voltversa/Advanced-Smart-Home-Hub/submission/Mahmoud_Mostafa_Adv_pcb/07_SmartHomeHub_Schematic_ERC_RevA.pdf

### Electrical Rules Check Report

Class | Document | Message
Warning | Sheet2.SchDoc | Off grid Pin F1-2 at 97.78mm,165mm
Warning | Sheet1.SchDoc | Off grid Pin IC1-3 at 55.08mm,25mm
Warning | Sheet1.SchDoc | Off grid Pin IC1-4 at 57.62mm,25mm
Warning | Sheet2.SchDoc | Off grid Pin C62-1 at 197.3mm,110mm
Warning | Sheet2.SchDoc | Off grid Pin D1-2 at 105mm,149.76mm
Warning | Sheet5.SchDoc | Off grid Pin D2-2 at 129.76mm,120mm
Warning | Sheet1.SchDoc | Off grid Pin IC1-5 at 60.16mm,25mm
Warning | Sheet1.SchDoc | Off grid Pin IC1-9 at 70.32mm,25mm
Warning | Sheet1.SchDoc | Off grid Pin IC1-10 at 72.86mm,25mm
Warning | Sheet1.SchDoc | Off grid Pin IC1-11 at 75.4mm,25mm
Warning | Sheet1.SchDoc | Off grid Pin IC1-6 at 62.7mm,25mm
Warning | Sheet1.SchDoc | Off grid Pin IC1-7 at 65.24mm,25mm
Warning | Sheet1.SchDoc | Off grid Pin IC1-8 at 67.78mm,25mm
Warning | Sheet2.SchDoc | Off grid Pin C61-1 at 252.7mm,145mm
Warning | Sheet3.SchDoc | Off grid Pin C51-1 at 160mm,62.3mm
Warning | Sheet3.SchDoc | Off grid Pin C52-1 at 170mm,62.3mm
Warning | Sheet2.SchDoc | Off grid Pin C53-1 at 70mm,107.3mm
Warning | Sheet2.SchDoc | Off grid Pin C48-1 at 60mm,107.3mm
Warning | Sheet3.SchDoc | Off grid Pin C49-1 at 140mm,62.3mm
Warning | Sheet3.SchDoc | Off grid Pin C50-1 at 150mm,62.3mm
Warning | Sheet5.SchDoc | Off grid Pin C54-1 at 30mm,82.3mm
Warning | Sheet3.SchDoc | Off grid Pin C58-1 at 190mm,62.3mm
Warning | Sheet6.SchDoc | Off grid Pin C59-2 at 80mm,69.92mm
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
Warning | Sheet1.SchDoc | Off grid Pin IC1-62 at 197.32mm,55.48mm
Warning | Sheet1.SchDoc | Off grid Pin IC1-66 at 197.32mm,65.64mm
Warning | Sheet1.SchDoc | Off grid Pin IC1-70 at 197.32mm,75.8mm
Warning | Sheet1.SchDoc | Off grid Pin IC1-71 at 197.32mm,78.34mm
Warning | Sheet1.SchDoc | Off grid Pin IC1-72 at 197.32mm,80.88mm
Warning | Sheet1.SchDoc | Off grid Pin IC1-67 at 197.32mm,68.18mm
Warning | Sheet1.SchDoc | Off grid Pin IC1-68 at 197.32mm,70.72mm
Warning | Sheet1.SchDoc | Off grid Pin IC1-69 at 197.32mm,73.26mm
Warning | Sheet1.SchDoc | Off grid Pin IC1-59 at 197.32mm,47.86mm
Warning | Sheet1.SchDoc | Off grid Pin IC1-48 at 169.38mm,25mm
Warning | Sheet1.SchDoc | Off grid Pin IC1-49 at 171.92mm,25mm
Warning | Sheet1.SchDoc | Off grid Pin IC1-50 at 174.46mm,25mm
Warning | Sheet1.SchDoc | Off grid Pin IC1-45 at 161.76mm,25mm
Warning | Sheet1.SchDoc | Off grid Pin IC1-46 at 164.3mm,25mm
Warning | Sheet1.SchDoc | Off grid Pin IC1-47 at 166.84mm,25mm
Warning | Sheet1.SchDoc | Off grid Pin IC1-52 at 179.54mm,25mm
Warning | Sheet1.SchDoc | Off grid Pin IC1-56 at 197.32mm,40.24mm
Warning | Sheet1.SchDoc | Off grid Pin IC1-57 at 197.32mm,42.78mm
Warning | Sheet1.SchDoc | Off grid Pin IC1-58 at 197.32mm,45.32mm
Warning | Sheet1.SchDoc | Off grid Pin IC1-53 at 197.32mm,32.62mm
Warning | Sheet1.SchDoc | Off grid Pin IC1-54 at 197.32mm,35.16mm
Warning | Sheet1.SchDoc | Off grid Pin IC1-55 at 197.32mm,37.7mm
Warning | Sheet1.SchDoc | Off grid Pin IC1-73 at 197.32mm,83.42mm
Warning | Sheet1.SchDoc | Off grid Pin IC1-91 at 197.32mm,129.14mm
Warning | Sheet1.SchDoc | Off grid Pin IC1-92 at 197.32mm,131.68mm
Warning | Sheet1.SchDoc | Off grid Pin IC1-93 at 197.32mm,134.22mm
Warning | Sheet1.SchDoc | Off grid Pin IC1-88 at 197.32mm,121.52mm
Warning | Sheet1.SchDoc | Off grid Pin IC1-89 at 197.32mm,124.06mm

Warning | Sheet1.SchDoc | Off grid Pin IC1-90 at 197.32mm,126.6mm
Warning | Sheet1.SchDoc | Off grid Pin IC1-94 at 197.32mm,136.76mm
Warning | Sheet1.SchDoc | Off grid Pin IC1-98 at 197.32mm,146.92mm
Warning | Sheet1.SchDoc | Off grid Pin IC1-99 at 197.32mm,149.46mm
Warning | Sheet1.SchDoc | Off grid Pin IC1-100 at 197.32mm,152mm
Warning | Sheet1.SchDoc | Off grid Pin IC1-95 at 197.32mm,139.3mm
Warning | Sheet1.SchDoc | Off grid Pin IC1-96 at 197.32mm,141.84mm
Warning | Sheet1.SchDoc | Off grid Pin IC1-97 at 197.32mm,144.38mm
Warning | Sheet1.SchDoc | Off grid Pin IC1-87 at 197.32mm,118.98mm
Warning | Sheet1.SchDoc | Off grid Pin IC1-77 at 197.32mm,93.58mm
Warning | Sheet1.SchDoc | Off grid Pin IC1-78 at 197.32mm,96.12mm
Warning | Sheet1.SchDoc | Off grid Pin IC1-79 at 197.32mm,98.66mm
Warning | Sheet1.SchDoc | Off grid Pin IC1-74 at 197.32mm,85.96mm
Warning | Sheet1.SchDoc | Off grid Pin IC1-75 at 197.32mm,88.5mm
Warning | Sheet1.SchDoc | Off grid Pin IC1-76 at 197.32mm,91.04mm
Warning | Sheet1.SchDoc | Off grid Pin IC1-80 at 197.32mm,101.2mm
Warning | Sheet1.SchDoc | Off grid Pin IC1-84 at 197.32mm,111.36mm
Warning | Sheet1.SchDoc | Off grid Pin IC1-85 at 197.32mm,113.9mm
Warning | Sheet1.SchDoc | Off grid Pin IC1-86 at 197.32mm,116.44mm
Warning | Sheet1.SchDoc | Off grid Pin IC1-81 at 197.32mm,103.74mm
Warning | Sheet1.SchDoc | Off grid Pin IC1-82 at 197.32mm,106.28mm
Warning | Sheet1.SchDoc | Off grid Pin IC1-83 at 197.32mm,108.82mm
Warning | Sheet1.SchDoc | Off grid Net Label SWO at 20mm,73.26mm
Warning | Sheet1.SchDoc | Off grid Net Label LCD_B3 at 20mm,103.74mm
Warning | Sheet5.SchDoc | Off grid Net Label LCD_B3 at 206.58mm,147.14mm
Warning | Sheet1.SchDoc | Off grid Net Label LCD_B4 at 20mm,40.24mm
Warning | Sheet5.SchDoc | Off grid Net Label LCD_B1 at 211.66mm,147.14mm
Warning | Sheet1.SchDoc | Off grid Net Label LCD_B2 at 20mm,124.06mm
Warning | Sheet5.SchDoc | Off grid Net Label LCD_B2 at 209.12mm,147.14mm
Warning | Sheet5.SchDoc | Off grid Net Label LCD_B4 at 204.04mm,147.14mm
Warning | Sheet5.SchDoc | Off grid Net Label LCD_B6 at 198.96mm,147.14mm
Warning | Sheet1.SchDoc | Off grid Net Label LCD_B7 at 20mm,80.88mm
Warning | Sheet5.SchDoc | Off grid Net Label LCD_B7 at 196.42mm,147.14mm
Warning | Sheet1.SchDoc | Off grid Net Label LCD_B5 at 174.46mm,11.68mm
Warning | Sheet5.SchDoc | Off grid Net Label LCD_B5 at 201.5mm,147.14mm
Warning | Sheet1.SchDoc | Off grid Net Label LCD_B6 at 20mm,83.42mm
Warning | Sheet1.SchDoc | Off grid Net Label LCD_B1 at 20mm,101.2mm
Warning | Sheet4.SchDoc | Off grid LED1 at 139.76mm,100mm
Warning | Sheet5.SchDoc | Off grid LED2 at 115.24mm,35mm
Warning | Sheet2.SchDoc | Off grid Net Label D+ at 30mm,144.52mm
Warning | Sheet2.SchDoc | Off grid C62 at 197.3mm,110mm
Warning | Sheet2.SchDoc | Off grid J4 at 19.84mm,139.44mm
Warning | Sheet2.SchDoc | Off grid L3 at 125.08mm,127.54mm
Warning | Sheet2.SchDoc | Off grid Net Label D- at 30mm,147.06mm
Warning | Sheet5.SchDoc | Off grid Net Label GND at 193.88mm,147.14mm
Warning | Sheet1.SchDoc | Off grid Net Label LCD_B0 at 55.08mm,15mm
Warning | Sheet5.SchDoc | Off grid Net Label LCD_B0 at 214.2mm,147.14mm
Warning | Sheet1.SchDoc | Off grid Net Label ESP_RX at 250mm,33.87mm
Warning | Sheet1.SchDoc | Off grid Net Label ESP_TX at 80.48mm,175mm
Warning | Sheet1.SchDoc | Off grid Net Label ESP_TX at 250mm,38.23mm
Warning | Sheet1.SchDoc | Off grid Net Label LCD_BL_CTRL at 90.64mm,170mm
Warning | Sheet5.SchDoc | Off grid Net Label LCD_G4 at 224.36mm,147.14mm
Warning | Sheet1.SchDoc | Off grid Net Label LCD_G5 at 210mm,129.14mm
Warning | Sheet5.SchDoc | Off grid Net Label LCD_G5 at 221.82mm,147.14mm
Warning | Sheet1.SchDoc | Off grid Net Label LCD_G3 at 20mm,106.28mm
Warning | Sheet5.SchDoc | Off grid Net Label LCD_G3 at 226.9mm,147.14mm
Warning | Sheet1.SchDoc | Off grid Net Label LCD_G4 at 200mm,126.6mm
Warning | Sheet1.SchDoc | Off grid Net Label LCD_G6 at 93.18mm,175mm
Warning | Sheet1.SchDoc | Off grid Net Label LCD_HSYNC at 77.94mm,10mm
Warning | Sheet5.SchDoc | Off grid Net Label LCD_HSYNC at 186.26mm,147.14mm
Warning | Sheet5.SchDoc | Off grid Net Label LCD_INT at 105.4mm,167.46mm
Warning | Sheet5.SchDoc | Off grid Net Label LCD_G6 at 219.28mm,147.14mm
Warning | Sheet1.SchDoc | Off grid Net Label LCD_G7 at 20mm,136.76mm
Warning | Sheet5.SchDoc | Off grid Net Label LCD_G7 at 216.74mm,147.14mm
Warning | Sheet5.SchDoc | Off grid Net Label LCD_G2 at 229.44mm,147.14mm
Warning | Sheet1.SchDoc | Off grid Net Label LCD_DCLK at 270mm,80.08mm
Warning | Sheet1.SchDoc | Off grid Net Label LCD_DE at 20mm,78.34mm
Warning | Sheet5.SchDoc | Off grid Net Label LCD_DE at 181.18mm,147.14mm

Warning | Sheet1.SchDoc | Off grid Net Label LCD_DCLK at 100.8mm,10mm
Warning | Sheet5.SchDoc | Off grid Net Label LCD_DCLK at 191.34mm,147.14mm
Warning | Sheet5.SchDoc | Off grid Net Label LCD_DCLK at 255mm,90.08mm
Warning | Sheet1.SchDoc | Off grid Net Label LCD_DISP at 20mm,96.12mm
Warning | Sheet1.SchDoc | Off grid Net Label LCD_G1 at 60.16mm,15mm
Warning | Sheet5.SchDoc | Off grid Net Label LCD_G1 at 231.98mm,147.14mm
Warning | Sheet1.SchDoc | Off grid Net Label LCD_G2 at 200mm,37.7mm
Warning | Sheet5.SchDoc | Off grid Net Label LCD_DISP at 188.8mm,147.14mm
Warning | Sheet1.SchDoc | Off grid Net Label LCD_G0 at 57.62mm,15mm
Warning | Sheet5.SchDoc | Off grid Net Label LCD_G0 at 234.52mm,147.14mm
Warning | Sheet2.SchDoc | Off grid C61 at 252.7mm,145mm
Warning | Sheet3.SchDoc | Off grid C15 at 70mm,62.3mm
Warning | Sheet3.SchDoc | Off grid C16 at 80mm,62.3mm
Warning | Sheet3.SchDoc | Off grid C17 at 90mm,62.3mm
Warning | Sheet3.SchDoc | Off grid C12 at 10mm,62.3mm
Warning | Sheet3.SchDoc | Off grid C13 at 50mm,62.3mm
Warning | Sheet3.SchDoc | Off grid C14 at 60mm,62.3mm
Warning | Sheet3.SchDoc | Off grid C18 at 100mm,62.3mm
Warning | Sheet6.SchDoc | Off grid C23 at 75mm,157.3mm
Warning | Sheet6.SchDoc | Off grid C24 at 160mm,154.76mm
Warning | Sheet6.SchDoc | Off grid C25 at 25mm,17.3mm
Warning | Sheet3.SchDoc | Off grid C19 at 110mm,62.3mm
Warning | Sheet3.SchDoc | Off grid C20 at 120mm,62.3mm
Warning | Sheet6.SchDoc | Off grid C21 at 102.7mm,125mm
Warning | Sheet3.SchDoc | Off grid C11 at 40mm,62.3mm
Warning | Sheet1.SchDoc | Nets Wire LCD_BL_CTRL has multiple names (Net Label LCD_BL_CTRL (2), Net Label
| | LCD_BL_CTRL_STM (2))
Warning | Sheet2.SchDoc | NetU1_5 contains Input Pin and Unspecified Port objects (Pin U1-5, Port PC10).
Warning | Sheet2.SchDoc | NetU1_6 contains Output Pin and Unspecified Port objects (Pin U1-6, Port PC11).
Warning | Sheet1.SchDoc | Net NetIC1_161 has no driving source (Pin IC1-161, Pin U1-5)
Warning | Sheet2.SchDoc | Net NetR24_2 has no driving source (Pin R24-2, Pin U1-4)
Warning | Sheet2.SchDoc | Net NetU1_10 has no driving source (Pin U1-10)
Warning | Sheet3.SchDoc | Off grid C2 at 50mm,102.3mm
Warning | Sheet3.SchDoc | Off grid C8 at 115mm,137.3mm
Warning | Sheet3.SchDoc | Off grid C9 at 20mm,62.3mm
Warning | Sheet3.SchDoc | Off grid C10 at 30mm,62.3mm
Warning | Sheet4.SchDoc | Off grid C4 at 85mm,107.3mm
Warning | Sheet3.SchDoc | Off grid C6 at 145mm,145.08mm
Warning | Sheet3.SchDoc | Off grid C7 at 160mm,145.08mm
Warning | Sheet6.SchDoc | Off grid C26 at 35mm,17.3mm
Warning | Sheet3.SchDoc | Off grid C50 at 150mm,62.3mm
Warning | Sheet3.SchDoc | Off grid C51 at 160mm,62.3mm
Warning | Sheet3.SchDoc | Off grid C52 at 170mm,62.3mm
Warning | Sheet2.SchDoc | Off grid C46 at 155mm,112.3mm
Warning | Sheet2.SchDoc | Off grid C48 at 60mm,107.3mm
Warning | Sheet3.SchDoc | Off grid C49 at 140mm,62.3mm
Warning | Sheet2.SchDoc | Off grid C53 at 70mm,107.3mm
Warning | Sheet6.SchDoc | Off grid C57 at 142.7mm,85mm
Warning | Sheet3.SchDoc | Off grid C58 at 190mm,62.3mm
Warning | Sheet2.SchDoc | Off grid C60 at 197.3mm,175mm
Warning | Sheet5.SchDoc | Off grid C54 at 30mm,82.3mm
Warning | Sheet6.SchDoc | Off grid C55 at 95mm,17.3mm
Warning | Sheet5.SchDoc | Off grid C56 at 115mm,137.3mm
Warning | Sheet4.SchDoc | Off grid C45 at 240mm,97.3mm
Warning | Sheet6.SchDoc | Off grid C30 at 80mm,17.3mm
Warning | Sheet4.SchDoc | Off grid C33 at 160mm,132.3mm
Warning | Sheet4.SchDoc | Off grid C36 at 170mm,132.3mm
Warning | Sheet6.SchDoc | Off grid C27 at 45mm,17.3mm
Warning | Sheet6.SchDoc | Off grid C28 at 55mm,17.3mm
Warning | Sheet6.SchDoc | Off grid C29 at 65mm,17.3mm
Warning | Sheet4.SchDoc | Off grid C37 at 75mm,112.3mm
Warning | Sheet2.SchDoc | Off grid C42 at 135mm,152.3mm
Warning | Sheet2.SchDoc | Off grid C43 at 117.7mm,135mm
Warning | Sheet4.SchDoc | Off grid C44 at 220mm,97.3mm
Warning | Sheet4.SchDoc | Off grid C39 at 180mm,32.3mm
Warning | Sheet4.SchDoc | Off grid C40 at 95mm,39.76mm
Warning | Sheet4.SchDoc | Off grid C41 at 30mm,37.3mm
Warning | Sheet5.SchDoc | Off grid Net Label LCD_INT at 171.02mm,147.14mm

Warning | Sheet1.SchDoc | Off grid Net Label SDRAM_D2 at 20mm,144.38mm
Warning | Sheet6.SchDoc | Off grid Net Label SDRAM_D2 at 185mm,132.38mm
Warning | Sheet1.SchDoc | Off grid Net Label SDRAM_D3 at 20mm,141.84mm
Warning | Sheet6.SchDoc | Off grid Net Label SDRAM_CS at 185mm,96.82mm
Warning | Sheet1.SchDoc | Off grid Net Label SDRAM_D0 at 151.6mm,169.78mm
Warning | Sheet1.SchDoc | Off grid Net Label SDRAM_D1 at 149.06mm,169.78mm
Warning | Sheet6.SchDoc | Off grid Net Label SDRAM_D3 at 185mm,127.3mm
Warning | Sheet1.SchDoc | Off grid Net Label SDRAM_D5 at 200mm,101.2mm
Warning | Sheet6.SchDoc | Off grid Net Label SDRAM_D6 at 185mm,117.14mm
Warning | Sheet1.SchDoc | Off grid Net Label SDRAM_D6 at 210mm,103.74mm
Warning | Sheet6.SchDoc | Off grid Net Label SDRAM_D4 at 185mm,124.76mm
Warning | Sheet1.SchDoc | Off grid Net Label SDRAM_D4 at 200mm,98.66mm
Warning | Sheet6.SchDoc | Off grid Net Label SDRAM_D5 at 185mm,119.68mm
Warning | Sheet1.SchDoc | Off grid Net Label SDRAM_CS at 141.44mm,12.78mm
Warning | Sheet6.SchDoc | Off grid Net Label SDRAM_BA1 at 185mm,91.74mm
Warning | Sheet1.SchDoc | Off grid Net Label SDRAM_CAS at 15mm,75.8mm
Warning | Sheet6.SchDoc | Off grid Net Label SDRAM_CAS at 185mm,101.9mm
Warning | Sheet6.SchDoc | Off grid Net Label SDRAM_A11 at 233.02mm,94.28mm
Warning | Sheet1.SchDoc | Off grid Net Label SDRAM_BA0 at 113.5mm,170mm
Warning | Sheet6.SchDoc | Off grid Net Label SDRAM_BA0 at 185mm,94.28mm
Warning | Sheet6.SchDoc | Off grid Net Label SDRAM_CKE at 153.02mm,29.92mm
Warning | Sheet6.SchDoc | Off grid Net Label SDRAM_CLK at 153.02mm,32.46mm
Warning | Sheet6.SchDoc | Off grid Net Label SDRAM_CLK at 233.02mm,101.9mm
Warning | Sheet1.SchDoc | Off grid Net Label SDRAM_CLK at 268.02mm,112.46mm
Warning | Sheet6.SchDoc | Off grid Net Label SDRAM_CKE at 233.02mm,99.36mm
Warning | Sheet1.SchDoc | Off grid Net Label SDRAM_CKE at 268.02mm,109.92mm
Warning | Sheet1.SchDoc | Off grid Net Label SDRAM_CLK at 103.34mm,175mm
Warning | Sheet6.SchDoc | Off grid Net Label SDRAM_D7 at 185mm,112.06mm
Warning | Sheet6.SchDoc | Off grid Net Label SDRAM_RAS at 155mm,34.92mm
Warning | Sheet6.SchDoc | Off grid Net Label SDRAM_RAS at 185mm,99.36mm
Warning | Sheet1.SchDoc | Off grid Net Label SDRAM_RAS at 200mm,75.8mm
Warning | Sheet1.SchDoc | Off grid Net Label SDRAM_D15 at 166.84mm,170mm
Warning | Sheet1.SchDoc | Off grid Net Label SDRAM_LDQM at 15mm,52.94mm
Warning | Sheet1.SchDoc | Off grid Net Label SDRAM_LDQM at 265mm,102.84mm
Warning | Sheet1.SchDoc | Off grid Net Label SDRAM_RAS at 270mm,114.92mm
Warning | Sheet1.SchDoc | Off grid Net Label SWCLK at 20mm,157.08mm
Warning | Sheet1.SchDoc | Off grid Net Label SWCLK at 250mm,21.77mm
Warning | Sheet1.SchDoc | Off grid Net Label SWDIO at 72.86mm,180mm
Warning | Sheet1.SchDoc | Off grid Net Label SDRAM_UDQM at 15mm,50.4mm
Warning | Sheet1.SchDoc | Off grid Net Label SDRAM_WE at 171.92mm,10mm
Warning | Sheet6.SchDoc | Off grid Net Label SDRAM_WE at 185mm,104.44mm
Warning | Sheet6.SchDoc | Off grid Net Label SDRAM_D14 at 233.02mm,134.92mm
Warning | Sheet1.SchDoc | Off grid Net Label SDRAM_D9 at 200mm,116.44mm
Warning | Sheet6.SchDoc | Off grid Net Label SDRAM_D9 at 233.02mm,117.14mm
Warning | Sheet6.SchDoc | Off grid Net Label SDRAM_D10 at 233.02mm,119.68mm
Warning | Sheet1.SchDoc | Off grid Net Label SDRAM_D7 at 200mm,111.36mm
Warning | Sheet1.SchDoc | Off grid Net Label SDRAM_D8 at 200mm,113.9mm
Warning | Sheet6.SchDoc | Off grid Net Label SDRAM_D8 at 233.02mm,112.06mm
Warning | Sheet1.SchDoc | Off grid Net Label SDRAM_D11 at 200mm,121.52mm
Warning | Sheet1.SchDoc | Off grid Net Label SDRAM_D13 at 171.92mm,170mm
Warning | Sheet6.SchDoc | Off grid Net Label SDRAM_D13 at 233.02mm,132.38mm
Warning | Sheet1.SchDoc | Off grid Net Label SDRAM_D14 at 169.38mm,170mm
Warning | Sheet6.SchDoc | Off grid Net Label SDRAM_D11 at 233.02mm,124.76mm
Warning | Sheet1.SchDoc | Off grid Net Label SDRAM_D12 at 200mm,124.06mm
Warning | Sheet6.SchDoc | Off grid Net Label SDRAM_D12 at 233.02mm,127.3mm
Warning | Sheet1.SchDoc | Off grid Net Label SDRAM_A11 at 200mm,96.12mm
Warning | Sheet1.SchDoc | Off grid Net Label LCD_R7 at 108.42mm,169.78mm
Warning | Sheet5.SchDoc | Off grid Net Label LCD_R7 at 237.06mm,147.14mm
Warning | Sheet5.SchDoc | Off grid Net Label LCD_RST at 105.4mm,162.38mm
Warning | Sheet5.SchDoc | Off grid Net Label LCD_R5 at 242.14mm,147.14mm
Warning | Sheet1.SchDoc | Off grid Net Label LCD_R6 at 200mm,55.48mm
Warning | Sheet5.SchDoc | Off grid Net Label LCD_R6 at 239.6mm,147.14mm
Warning | Sheet5.SchDoc | Off grid Net Label LCD_RST at 173.56mm,147.14mm
Warning | Sheet5.SchDoc | Off grid Net Label LCD_SCL at 105.4mm,152.22mm
Warning | Sheet5.SchDoc | Off grid Net Label LCD_SCL at 168.48mm,147.14mm
Warning | Sheet5.SchDoc | Off grid Net Label LCD_SCL at 255mm,39.92mm
Warning | Sheet1.SchDoc | Off grid Net Label LCD_RST at 200mm,42.78mm
Warning | Sheet1.SchDoc | Off grid Net Label LCD_RST at 245mm,47.38mm

Warning | Sheet5.SchDoc | Off grid Net Label LCD_RST at 255mm,32.3mm
Warning | Sheet1.SchDoc | Off grid Net Label LCD_R5 at 136.36mm,5mm
Warning | Sheet1.SchDoc | Off grid Net Label LCD_R0 at 20mm,98.66mm
Warning | Sheet5.SchDoc | Off grid Net Label LCD_R0 at 254.84mm,147.14mm
Warning | Sheet1.SchDoc | Off grid Net Label LCD_R1 at 200mm,63.1mm
Warning | Sheet1.SchDoc | Off grid Net Label LCD_INT at 205mm,45.32mm
Warning | Sheet1.SchDoc | Off grid Net Label LCD_INT at 245mm,49.92mm
Warning | Sheet5.SchDoc | Off grid Net Label LCD_INT at 255mm,34.84mm
Warning | Sheet5.SchDoc | Off grid Net Label LCD_R1 at 252.3mm,147.14mm
Warning | Sheet5.SchDoc | Off grid Net Label LCD_R3 at 247.22mm,147.14mm
Warning | Sheet1.SchDoc | Off grid Net Label LCD_R4 at 77.94mm,175mm
Warning | Sheet5.SchDoc | Off grid Net Label LCD_R4 at 244.68mm,147.14mm
Warning | Sheet1.SchDoc | Off grid Net Label LCD_R2 at 200mm,65.64mm
Warning | Sheet5.SchDoc | Off grid Net Label LCD_R2 at 249.76mm,147.14mm
Warning | Sheet1.SchDoc | Off grid Net Label LCD_R3 at 200mm,52.94mm
Warning | Sheet1.SchDoc | Off grid Net Label LCD_SDA at 20mm,55.48mm
Warning | Sheet1.SchDoc | Off grid Net Label SDRAM_A5 at 108.42mm,10mm
Warning | Sheet6.SchDoc | Off grid Net Label SDRAM_A5 at 233.02mm,81.58mm
Warning | Sheet1.SchDoc | Off grid Net Label SDRAM_A6 at 205mm,78.34mm
Warning | Sheet6.SchDoc | Off grid Net Label SDRAM_A2 at 185mm,81.58mm
Warning | Sheet1.SchDoc | Off grid Net Label SDRAM_A3 at 103.34mm,10mm
Warning | Sheet1.SchDoc | Off grid Net Label SDRAM_A4 at 105.88mm,10mm
Warning | Sheet6.SchDoc | Off grid Net Label SDRAM_A6 at 233.02mm,84.12mm
Warning | Sheet6.SchDoc | Off grid Net Label SDRAM_A9 at 233.02mm,91.74mm
Warning | Sheet6.SchDoc | Off grid Net Label SDRAM_A10 at 185mm,89.2mm
Warning | Sheet1.SchDoc | Off grid Net Label SDRAM_A10 at 200mm,93.58mm
Warning | Sheet6.SchDoc | Off grid Net Label SDRAM_A7 at 233.02mm,86.66mm
Warning | Sheet1.SchDoc | Off grid Net Label SDRAM_A8 at 200mm,88.5mm
Warning | Sheet6.SchDoc | Off grid Net Label SDRAM_A8 at 233.02mm,89.2mm
Warning | Sheet1.SchDoc | Off grid Net Label SDRAM_A2 at 93.18mm,10mm
Warning | Sheet5.SchDoc | Off grid Net Label LCD_VSYNC at 183.72mm,147.14mm
Warning | Sheet1.SchDoc | Off grid Net Label NRST at 133.82mm,15mm
Warning | Sheet1.SchDoc | Off grid Net Label QSPI_D0 at 121.12mm,10mm
Warning | Sheet5.SchDoc | Off grid Net Label LCD_SDA at 105.4mm,157.3mm
Warning | Sheet5.SchDoc | Off grid Net Label LCD_SDA at 165.94mm,147.14mm
Warning | Sheet1.SchDoc | Off grid Net Label LCD_VSYNC at 75.4mm,10mm
Warning | Sheet1.SchDoc | Off grid Net Label QSPI_D1 at 123.66mm,10mm
Warning | Sheet6.SchDoc | Off grid Net Label SDRAM_A0 at 185mm,86.66mm
Warning | Sheet1.SchDoc | Off grid Net Label SDRAM_A1 at 90.64mm,10mm
Warning | Sheet6.SchDoc | Off grid Net Label SDRAM_A1 at 185mm,84.12mm
Warning | Sheet1.SchDoc | Off grid Net Label QSPI_D2 at 118.58mm,10mm
Warning | Sheet1.SchDoc | Off grid Net Label QSPI_NCS at 20mm,65.64mm
Warning | Sheet1.SchDoc | Off grid Net Label SDRAM_A0 at 88.1mm,10mm
Warning | Sheet1.SchDoc | Off grid Pin IC1-157 at 32.22mm,162.16mm
Warning | Sheet6.SchDoc | Off grid Port ESP_TX at 160mm,56.79mm
Warning | Sheet1.SchDoc | Off grid Port ESP_TX at 231.79mm,37.98mm
Warning | Sheet4.SchDoc | Off grid Port Flamesensor_A0 at 9.46mm,50mm
Warning | Sheet1.SchDoc | Off grid Port CO2_SDA at 197.32mm,157.08mm
Warning | Sheet6.SchDoc | Off grid Port ESP_RX at 110mm,61.66mm
Warning | Sheet1.SchDoc | Off grid Port ESP_RX at 231.66mm,33.87mm
Warning | Sheet4.SchDoc | Off grid Port Flamesensor_A0 at 109.46mm,49.92mm
Warning | Sheet1.SchDoc | Off grid Port Flamesensor_D0 at 164.3mm,4.46mm
Warning | Sheet5.SchDoc | Off grid Port LCD_B[0..7] at 217.88mm,100mm
Warning | Sheet1.SchDoc | Off grid Port LCD_B[0..7] at 232.88mm,85mm
Warning | Sheet1.SchDoc | Off grid Port Flamesensor_A0 at 159.22mm,4.46mm
Warning | Sheet4.SchDoc | Off grid Port Flamesensor_D0 at 89.46mm,25mm
Warning | Sheet4.SchDoc | Off grid Port Flamesensor_D0 at 94.46mm,80mm
Warning | Sheet4.SchDoc | Off grid Port CO2_SDA at 115mm,155.32mm
Warning | Sheet6.SchDoc | Off grid Pin Y2-3 at 208.1mm,170mm
Warning | Sheet1.SchDoc | Off grid Port BME_SCL at 197.32mm,144.38mm
Warning | Sheet1.SchDoc | Off grid Port BME_SDA at 197.32mm,146.92mm
Warning | Sheet4.SchDoc | Off grid Pin VR1-S1 at 93.02mm,52.54mm
Warning | Sheet6.SchDoc | Off grid Pin Y1-2 at 65.16mm,170mm
Warning | Sheet6.SchDoc | Off grid Pin Y2-2 at 208.1mm,167.46mm
Warning | Sheet1.SchDoc | Off grid Port BUZZER at 123.66mm,169.78mm
Warning | Sheet3.SchDoc | Off grid Port cap2 at 130.69mm,150mm
Warning | Sheet4.SchDoc | Off grid Port CO2_SCL at 115mm,152.78mm
Warning | Sheet1.SchDoc | Off grid Port CO2_SCL at 197.32mm,154.54mm

Warning | Sheet3.SchDoc | Off grid Port cap1 at 150.87mm,147.7mm
Warning | Sheet1.SchDoc | Off grid Port cap1 at 197.32mm,131.68mm
Warning | Sheet1.SchDoc | Off grid Port cap2 at 70.32mm,169.78mm
Warning | Sheet1.SchDoc | Off grid Port LCD_BL_CTRL at 229.3mm,45mm
Warning | Sheet5.SchDoc | Off grid Port LCD_SCL at 240.03mm,39.92mm
Warning | Sheet1.SchDoc | Off grid Port LCD_SDA at 229.62mm,57.54mm
Warning | Sheet5.SchDoc | Off grid Port LCD_SDA at 239.62mm,42.46mm
Warning | Sheet1.SchDoc | Off grid Port LCD_R[0..7] at 232.88mm,95mm
Warning | Sheet1.SchDoc | Off grid Port LCD_RST at 230.04mm,47.38mm
Warning | Sheet5.SchDoc | Off grid Port LCD_RST at 240.04mm,32.3mm
Warning | Sheet5.SchDoc | Off grid Port LCD_VSYNC at 211.49mm,80mm
Warning | Sheet1.SchDoc | Off grid Port OSC32_IN at 70.32mm,9.63mm
Warning | Sheet1.SchDoc | Off grid Port OSC32_OUT at 72.86mm,7.36mm
Warning | Sheet1.SchDoc | Off grid Port OSC_HSE_IN at 128.74mm,6.44mm
Warning | Sheet1.SchDoc | Off grid Port LCD_VSYNC at 226.49mm,70mm
Warning | Sheet1.SchDoc | Off grid Port NRST at 254.11mm,15mm
Warning | Sheet6.SchDoc | Off grid Port OSC32_IN at 19.63mm,170mm
Warning | Sheet5.SchDoc | Off grid Port LCD_R[0..7] at 217.88mm,110mm
Warning | Sheet5.SchDoc | Off grid Port LCD_DE at 216.18mm,75mm
Warning | Sheet1.SchDoc | Off grid Port LCD_DE at 231.18mm,65mm
Warning | Sheet5.SchDoc | Off grid Port LCD_DISP at 214.3mm,70mm
Warning | Sheet5.SchDoc | Off grid Port LCD_BL_CTRL at 234.3mm,30mm
Warning | Sheet5.SchDoc | Off grid Port LCD_DCLK at 212.92mm,90mm
Warning | Sheet1.SchDoc | Off grid Port LCD_DCLK at 227.92mm,80mm
Warning | Sheet1.SchDoc | Off grid Port LCD_DISP at 229.3mm,60mm
Warning | Sheet1.SchDoc | Off grid Port LCD_HSYNC at 226.49mm,75mm
Warning | Sheet1.SchDoc | Off grid Port LCD_INT at 230.42mm,49.92mm
Warning | Sheet5.SchDoc | Off grid Port LCD_INT at 240.42mm,34.84mm
Warning | Sheet5.SchDoc | Off grid Port LCD_G[0..7] at 217.75mm,105mm
Warning | Sheet1.SchDoc | Off grid Port LCD_G[0..7] at 232.75mm,90mm
Warning | Sheet5.SchDoc | Off grid Port LCD_HSYNC at 211.49mm,85mm
Warning | Sheet2.SchDoc | Off grid Pin U1-14 at 192.06mm,153.02mm
Warning | Sheet1.SchDoc | Off grid Pin R2-2 at 15mm,37.78mm
Warning | Sheet1.SchDoc | Off grid Pin R3-1 at 247.78mm,15mm
Warning | Sheet6.SchDoc | Off grid Pin R4-1 at 175mm,62.78mm
Warning | Sheet4.SchDoc | Off grid Pin Q1-1 at 45mm,24.76mm
Warning | Sheet1.SchDoc | Off grid Pin R1-1 at 14.44mm,78.34mm
Warning | Sheet1.SchDoc | Off grid Pin R1-2 at 14.44mm,60.56mm
Warning | Sheet3.SchDoc | Off grid Pin R5-1 at 35mm,117.22mm
Warning | Sheet4.SchDoc | Off grid Pin R9-2 at 110mm,177.78mm
Warning | Sheet4.SchDoc | Off grid Pin R10-1 at 245mm,144.92mm
Warning | Sheet4.SchDoc | Off grid Pin R10-2 at 245mm,162.7mm
Warning | Sheet6.SchDoc | Off grid Pin R6-1 at 72.78mm,130mm
Warning | Sheet5.SchDoc | Off grid Pin R7-1 at 240mm,52.22mm
Warning | Sheet5.SchDoc | Off grid Pin R8-1 at 120mm,72.22mm
Warning | Sheet5.SchDoc | Off grid Pin P3-2 at 25mm,29.92mm
Warning | Sheet6.SchDoc | Off grid Pin P1-6 at 145.32mm,72.54mm
Warning | Sheet6.SchDoc | Off grid Pin P1-8 at 145.32mm,70mm
Warning | Sheet6.SchDoc | Off grid Pin P2-1 at 44.68mm,87.54mm
Warning | Sheet6.SchDoc | Off grid Pin P1-2 at 145.32mm,77.62mm
Warning | Sheet6.SchDoc | Off grid Pin P1-3 at 125mm,75.08mm
Warning | Sheet6.SchDoc | Off grid Pin P1-4 at 145.32mm,75.08mm
Warning | Sheet6.SchDoc | Off grid Pin P2-3 at 44.68mm,85mm
Warning | Sheet6.SchDoc | Off grid Pin P2-9 at 44.68mm,77.38mm
Warning | Sheet6.SchDoc | Off grid Pin P2-10 at 65mm,77.38mm
Warning | Sheet5.SchDoc | Off grid Pin P3-1 at 25mm,27.38mm
Warning | Sheet6.SchDoc | Off grid Pin P2-5 at 44.68mm,82.46mm
Warning | Sheet6.SchDoc | Off grid Pin P2-7 at 44.68mm,79.92mm
Warning | Sheet6.SchDoc | Off grid Pin P2-8 at 65mm,79.92mm
Warning | Sheet4.SchDoc | Off grid Pin R11-2 at 110mm,152.78mm
Warning | Sheet2.SchDoc | Off grid Pin U1-3 at 192.06mm,122.54mm
Warning | Sheet2.SchDoc | Off grid Pin U1-5 at 220mm,147.94mm
Warning | Sheet2.SchDoc | Off grid Pin U1-6 at 192.06mm,140.32mm
Warning | Sheet4.SchDoc | Off grid Pin R25-2 at 109.46mm,49.92mm
Warning | Sheet6.SchDoc | Off grid Pin R26-1 at 195mm,47.78mm
Warning | Sheet2.SchDoc | Off grid Pin U1-2 at 192.06mm,120mm
Warning | Sheet2.SchDoc | Off grid Pin U1-7 at 192.06mm,125.08mm
Warning | Sheet2.SchDoc | Off grid Pin U1-11 at 220mm,132.7mm

Warning | Sheet2.SchDoc | Off grid Pin U1-12 at 220mm,127.62mm
Warning | Sheet2.SchDoc | Off grid Pin U1-13 at 220mm,125.08mm
Warning | Sheet2.SchDoc | Off grid Pin U1-8 at 192.06mm,127.62mm
Warning | Sheet2.SchDoc | Off grid Pin U1-9 at 220mm,142.86mm
Warning | Sheet2.SchDoc | Off grid Pin U1-10 at 220mm,137.78mm
Warning | Sheet4.SchDoc | Off grid Pin R25-1 at 109.46mm,32.14mm
Warning | Sheet4.SchDoc | Off grid Pin R15-1 at 117.22mm,100mm
Warning | Sheet5.SchDoc | Off grid Pin R16-2 at 67.78mm,70mm
Warning | Sheet5.SchDoc | Off grid Pin R17-2 at 270mm,60.24mm
Warning | Sheet4.SchDoc | Off grid Pin R12-1 at 230mm,122.22mm
Warning | Sheet4.SchDoc | Off grid Pin R13-1 at 137.78mm,90mm
Warning | Sheet4.SchDoc | Off grid Pin R14-2 at 45mm,52.22mm
Warning | Sheet5.SchDoc | Off grid Pin R18-1 at 280mm,42.22mm
Warning | Sheet2.SchDoc | Off grid Pin R22-1 at 40mm,157.78mm
Warning | Sheet2.SchDoc | Off grid Pin R23-1 at 50mm,152.78mm
Warning | Sheet2.SchDoc | Off grid Pin R24-1 at 220mm,170.8mm
Warning | Sheet5.SchDoc | Off grid Pin R19-1 at 92.78mm,35mm
Warning | Sheet4.SchDoc | Off grid Pin R20-1 at 202.22mm,70mm
Warning | Sheet4.SchDoc | Off grid Pin R21-1 at 220mm,52.22mm
Warning | Sheet6.SchDoc | Off grid Port OSC_HSE_IN at 208.1mm,170mm
Warning | Sheet1.SchDoc | Off grid Power Object GND at 156.68mm,169.78mm
Warning | Sheet4.SchDoc | Off grid Power Object GND at 160mm,132.3mm
Warning | Sheet6.SchDoc | Off grid Power Object GND at 185mm,114.6mm
Warning | Sheet3.SchDoc | Off grid Power Object GND at 115mm,137.3mm
Warning | Sheet1.SchDoc | Off grid Power Object GND at 128.74mm,169.78mm
Warning | Sheet1.SchDoc | Off grid Power Object GND at 149.06mm,25mm
Warning | Sheet6.SchDoc | Off grid Power Object GND at 195mm,47.78mm
Warning | Sheet1.SchDoc | Off grid Power Object GND at 197.32mm,106.28mm
Warning | Sheet1.SchDoc | Off grid Power Object GND at 197.32mm,134.22mm
Warning | Sheet6.SchDoc | Off grid Power Object GND at 208.1mm,167.46mm
Warning | Sheet2.SchDoc | Off grid Power Object GND at 197.3mm,110mm
Warning | Sheet1.SchDoc | Off grid Power Object GND at 197.32mm,50.4mm
Warning | Sheet1.SchDoc | Off grid Power Object GND at 197.32mm,80.88mm
Warning | Sheet2.SchDoc | Off grid Power Object GND at 105mm,149.76mm
Warning | Sheet1.SchDoc | Off grid Power Object 3V3 at 197.32mm,136.76mm
Warning | Sheet1.SchDoc | Off grid Power Object 3V3 at 197.32mm,159.62mm
Warning | Sheet6.SchDoc | Off grid Power Object 3V3 at 245mm,114.6mm
Warning | Sheet1.SchDoc | Off grid Power Object 3V3 at 197.32mm,47.86mm
Warning | Sheet1.SchDoc | Off grid Power Object 3V3 at 197.32mm,83.42mm
Warning | Sheet1.SchDoc | Off grid Power Object 3V3 at 197.32mm,108.82mm
Warning | Sheet5.SchDoc | Off grid Power Object 3V3 at 257.38mm,140mm
Warning | Sheet1.SchDoc | Off grid Power Object GND at 67.78mm,169.78mm
Warning | Sheet6.SchDoc | Off grid Power Object GND at 80mm,67.3mm
Warning | Sheet1.SchDoc | Off grid Power Object GND at 100.8mm,169.78mm
Warning | Sheet2.SchDoc | Off grid Power Object +5 at 236.98mm,127.54mm
Warning | Sheet1.SchDoc | Off grid Power Object GND at 32.22mm,93.58mm
Warning | Sheet1.SchDoc | Off grid Power Object GND at 32.22mm,129.14mm
Warning | Sheet4.SchDoc | Off grid Power Object GND at 235mm,97.3mm
Warning | Sheet4.SchDoc | Off grid R20 at 202.22mm,70mm
Warning | Sheet4.SchDoc | Off grid R21 at 220mm,52.22mm
Warning | Sheet2.SchDoc | Off grid R22 at 40mm,157.78mm
Warning | Sheet4.SchDoc | Off grid R15 at 117.22mm,100mm
Warning | Sheet5.SchDoc | Off grid R18 at 280mm,42.22mm
Warning | Sheet5.SchDoc | Off grid R19 at 92.78mm,35mm
Warning | Sheet2.SchDoc | Off grid R23 at 50mm,152.78mm
Warning | Sheet2.SchDoc | Off sheet +5 at -30mm,210mm
Warning | Sheet2.SchDoc | Off sheet GND at -10mm,210mm
Warning | Sheet2.SchDoc | Unconnected Pin U1-10 at 220mm,137.78mm
Warning | Sheet2.SchDoc | Off grid R24 at 220mm,170.8mm
Warning | Sheet4.SchDoc | Off grid R25 at 109.46mm,32.14mm
Warning | Sheet6.SchDoc | Off grid R26 at 195mm,47.78mm
Warning | Sheet4.SchDoc | Off grid R13 at 137.78mm,90mm
Warning | Sheet3.SchDoc | Off grid Power Object VDDA at 88.7mm,150.32mm
Warning | Sheet1.SchDoc | Off grid R1 at 14.44mm,78.34mm
Warning | Sheet1.SchDoc | Off grid R3 at 247.78mm,15mm
Warning | Sheet5.SchDoc | Off grid Power Object GND at 240mm,52.22mm
Warning | Sheet6.SchDoc | Off grid Power Object GND at 245mm,109.52mm
Warning | Sheet6.SchDoc | Off grid Power Object GND at 245mm,122.22mm

Warning | Sheet6.SchDoc | Off grid R4 at 175mm,62.78mm
Warning | Sheet5.SchDoc | Off grid R8 at 120mm,72.22mm
Warning | Sheet4.SchDoc | Off grid R10 at 245mm,144.92mm
Warning | Sheet4.SchDoc | Off grid R12 at 230mm,122.22mm
Warning | Sheet3.SchDoc | Off grid R5 at 35mm,117.22mm
Warning | Sheet6.SchDoc | Off grid R6 at 72.78mm,130mm
Warning | Sheet5.SchDoc | Off grid R7 at 240mm,52.22mm
Warning | Sheet6.SchDoc | Off grid Power Object 3V3 at 185mm,122.22mm
Warning | Sheet1.SchDoc | Off grid Port QSPI_NCS at 244.46mm,155mm
Warning | Sheet6.SchDoc | Off grid Port SDRAM_BA0 at 136.36mm,10mm
Warning | Sheet1.SchDoc | Off grid Port SDRAM_BA0 at 241.36mm,130mm
Warning | Sheet1.SchDoc | Off grid Port QSPI_CLK at 244.2mm,160mm
Warning | Sheet6.SchDoc | Off grid Port QSPI_D0 at 95mm,109.92mm
Warning | Sheet6.SchDoc | Off grid Port QSPI_NCS at 29.46mm,120mm
Warning | Sheet6.SchDoc | Off grid Port SDRAM_BA1 at 136.56mm,15mm
Warning | Sheet6.SchDoc | Off grid Port SDRAM_CKE at 134.1mm,29.92mm
Warning | Sheet1.SchDoc | Off grid Port SDRAM_CKE at 249.1mm,109.92mm
Warning | Sheet6.SchDoc | Off grid Port SDRAM_CLK at 134.03mm,32.46mm
Warning | Sheet1.SchDoc | Off grid Port SDRAM_BA1 at 241.56mm,135mm
Warning | Sheet6.SchDoc | Off grid Port SDRAM_CAS at 131.28mm,37.46mm
Warning | Sheet1.SchDoc | Off grid Port SDRAM_CAS at 246.28mm,117.46mm
Warning | Sheet1.SchDoc | Off grid Port PI3 at 16.09mm,162.16mm
Warning | Sheet6.SchDoc | Off grid Port PC11 at 60.1mm,65mm
Warning | Sheet2.SchDoc | Off grid Port PC11 at 175.1mm,140mm
Warning | Sheet1.SchDoc | Off grid Port PC12 at 22.14mm,146.92mm
Warning | Sheet1.SchDoc | Off grid Port PC10 at 22.12mm,152mm
Warning | Sheet2.SchDoc | Off grid Port PC10 at 220mm,147.94mm
Warning | Sheet1.SchDoc | Off grid Port PC11 at 20.1mm,150mm
Warning | Sheet1.SchDoc | Off grid Port PH14 at 60.16mm,175mm
Warning | Sheet1.SchDoc | Off grid Port PH15 at 62.7mm,175mm
Warning | Sheet6.SchDoc | Off grid Port PI0 at 25mm,79.92mm
Warning | Sheet1.SchDoc | Off grid Port PI0 at 55.08mm,175mm
Warning | Sheet6.SchDoc | Off grid Port PH14 at 69.77mm,90mm
Warning | Sheet6.SchDoc | Off grid Port PH15 at 25mm,77.38mm
Warning | Sheet1.SchDoc | Off grid Port PH15 at 57.62mm,175mm
Warning | Sheet1.SchDoc | Off grid Port SDRAM_CLK at 249.03mm,112.46mm
Warning | Sheet1.SchDoc | Off grid Power Object 3V3 at 32.22mm,159.62mm
Warning | Sheet3.SchDoc | Off grid Power Object 3V3 at 63.7mm,150.32mm
Warning | Sheet1.SchDoc | Off grid Power Object 3V3 at 65.24mm,169.78mm
Warning | Sheet1.SchDoc | Off grid Power Object 3V3 at 32.22mm,42.78mm
Warning | Sheet1.SchDoc | Off grid Power Object 3V3 at 32.22mm,91.04mm
Warning | Sheet1.SchDoc | Off grid Power Object 3V3 at 32.22mm,126.6mm
Warning | Sheet1.SchDoc | Off grid Power Object 3V3 at 85.56mm,25mm
Warning | Sheet1.SchDoc | Off grid Power Object 3V3 at 146.52mm,25mm
Warning | Sheet1.SchDoc | Off grid Power Object 3V3 at 154.14mm,169.78mm
Warning | Sheet6.SchDoc | Off grid Power Object 3V3 at 185mm,109.52mm
Warning | Sheet1.SchDoc | Off grid Power Object 3V3 at 98.26mm,169.78mm
Warning | Sheet1.SchDoc | Off grid Power Object 3V3 at 113.5mm,25mm
Warning | Sheet1.SchDoc | Off grid Power Object 3V3 at 131.28mm,169.78mm
Warning | Sheet3.SchDoc | Off grid Power Object 3V3 at 22.46mm,173.1mm
Warning | Sheet6.SchDoc | Off grid Port SDRAM_RAS at 131.28mm,34.92mm
Warning | Sheet1.SchDoc | Off grid Port SDRAM_RAS at 246.28mm,114.92mm
Warning | Sheet6.SchDoc | Off grid Port SDRAM_WE at 131.56mm,40mm
Warning | Sheet6.SchDoc | Off grid Port SDRAM_CS at 131.56mm,45mm
Warning | Sheet1.SchDoc | Off grid Port SDRAM_CS at 246.56mm,125mm
Warning | Sheet1.SchDoc | Off grid Port SDRAM_LDQM at 238.91mm,102.84mm
Warning | Sheet1.SchDoc | Off grid Port SDRAM_WE at 246.56mm,120mm
Warning | Sheet1.SchDoc | Off grid Port SWDIO at 232.49mm,25.64mm
Warning | Sheet2.SchDoc | Off grid Port SWO at 86.25mm,60mm
Warning | Sheet1.SchDoc | Off grid Port SWO at 231.25mm,29.75mm
Warning | Sheet5.SchDoc | Off grid Port sw at 52.39mm,85mm
Warning | Sheet2.SchDoc | Off grid Port SWCLK at 91.87mm,65mm
Warning | Sheet1.SchDoc | Off grid Port SWCLK at 231.87mm,21.52mm
Warning | Sheet6.SchDoc | Off grid Pin P1-1 at 125mm,77.62mm
Warning | Sheet6.SchDoc | Off grid Pin IC2-28 at 233.02mm,76.5mm
Warning | Sheet6.SchDoc | Off grid Pin IC2-30 at 233.02mm,81.58mm
Warning | Sheet6.SchDoc | Off grid Pin IC2-31 at 233.02mm,84.12mm
Warning | Sheet6.SchDoc | Off grid Pin IC2-24 at 200mm,84.12mm

Warning | Sheet6.SchDoc | Off grid Pin IC2-25 at 200mm,81.58mm
Warning | Sheet6.SchDoc | Off grid Pin IC2-27 at 200mm,76.5mm
Warning | Sheet6.SchDoc | Off grid Pin IC2-32 at 233.02mm,86.66mm
Warning | Sheet6.SchDoc | Off grid Pin IC2-36 at 233.02mm,96.82mm
Warning | Sheet6.SchDoc | Off grid Pin IC2-37 at 233.02mm,99.36mm
Warning | Sheet6.SchDoc | Off grid Pin IC2-38 at 233.02mm,101.9mm
Warning | Sheet6.SchDoc | Off grid Pin IC2-33 at 233.02mm,89.2mm
Warning | Sheet6.SchDoc | Off grid Pin IC2-34 at 233.02mm,91.74mm
Warning | Sheet6.SchDoc | Off grid Pin IC2-35 at 233.02mm,94.28mm
Warning | Sheet6.SchDoc | Off grid Pin IC2-23 at 200mm,86.66mm
Warning | Sheet6.SchDoc | Off grid Pin IC2-12 at 200mm,114.6mm
Warning | Sheet6.SchDoc | Off grid Pin IC2-13 at 200mm,112.06mm
Warning | Sheet6.SchDoc | Off grid Pin IC2-14 at 200mm,109.52mm
Warning | Sheet6.SchDoc | Off grid Pin IC2-9 at 200mm,122.22mm
Warning | Sheet6.SchDoc | Off grid Pin IC2-10 at 200mm,119.68mm
Warning | Sheet6.SchDoc | Off grid Pin IC2-11 at 200mm,117.14mm
Warning | Sheet6.SchDoc | Off grid Pin IC2-16 at 200mm,104.44mm
Warning | Sheet6.SchDoc | Off grid Pin IC2-20 at 200mm,94.28mm
Warning | Sheet6.SchDoc | Off grid Pin IC2-21 at 200mm,91.74mm
Warning | Sheet6.SchDoc | Off grid Pin IC2-22 at 200mm,89.2mm
Warning | Sheet6.SchDoc | Off grid Pin IC2-17 at 200mm,101.9mm
Warning | Sheet6.SchDoc | Off grid Pin IC2-18 at 200mm,99.36mm
Warning | Sheet6.SchDoc | Off grid Pin IC2-19 at 200mm,96.82mm
Warning | Sheet6.SchDoc | Off grid Pin IC2-39 at 233.02mm,104.44mm
Warning | Sheet4.SchDoc | Off grid Pin IC3-7 at 97.94mm,147.7mm
Warning | Sheet4.SchDoc | Off grid Pin IC3-8 at 97.94mm,150.24mm
Warning | Sheet4.SchDoc | Off grid Pin IC3-9 at 97.94mm,152.78mm
Warning | Sheet4.SchDoc | Off grid Pin IC3-4 at 77.62mm,135mm
Warning | Sheet4.SchDoc | Off grid Pin IC3-5 at 80.16mm,135mm
Warning | Sheet4.SchDoc | Off grid Pin IC3-6 at 97.94mm,145.16mm
Warning | Sheet4.SchDoc | Off grid Pin IC3-10 at 97.94mm,155.32mm
Warning | Sheet4.SchDoc | Off grid Pin IC3-14 at 72.54mm,168.02mm
Warning | Sheet4.SchDoc | Off grid Pin IC3-16 at 52.22mm,157.86mm
Warning | Sheet4.SchDoc | Off grid Pin IC3-17 at 52.22mm,155.32mm
Warning | Sheet4.SchDoc | Off grid Pin IC3-11 at 80.16mm,168.02mm
Warning | Sheet4.SchDoc | Off grid Pin IC3-12 at 77.62mm,168.02mm
Warning | Sheet4.SchDoc | Off grid Pin IC3-13 at 75.08mm,168.02mm
Warning | Sheet4.SchDoc | Off grid Pin IC3-3 at 75.08mm,135mm
Warning | Sheet6.SchDoc | Off grid Pin IC2-44 at 233.02mm,117.14mm
Warning | Sheet6.SchDoc | Off grid Pin IC2-45 at 233.02mm,119.68mm
Warning | Sheet6.SchDoc | Off grid Pin IC2-46 at 233.02mm,122.22mm
Warning | Sheet6.SchDoc | Off grid Pin IC2-41 at 233.02mm,109.52mm
Warning | Sheet6.SchDoc | Off grid Pin IC2-42 at 233.02mm,112.06mm
Warning | Sheet6.SchDoc | Off grid Pin IC2-43 at 233.02mm,114.6mm
Warning | Sheet6.SchDoc | Off grid Pin IC2-47 at 233.02mm,124.76mm
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
Warning | Sheet5.SchDoc | Off grid Pin J2-30 at 191.34mm,147.14mm
Warning | Sheet5.SchDoc | Off grid Pin J2-31 at 188.8mm,147.14mm
Warning | Sheet5.SchDoc | Off grid Pin J2-26 at 201.5mm,147.14mm
Warning | Sheet5.SchDoc | Off grid Pin J2-27 at 198.96mm,147.14mm

Warning | Sheet5.SchDoc | Off grid Pin J2-28 at 196.42mm,147.14mm
Warning | Sheet5.SchDoc | Off grid Pin J2-18 at 221.82mm,147.14mm
Warning | Sheet5.SchDoc | Off grid Pin J2-8 at 247.22mm,147.14mm
Warning | Sheet5.SchDoc | Off grid Pin J2-9 at 244.68mm,147.14mm
Warning | Sheet5.SchDoc | Off grid Pin J2-10 at 242.14mm,147.14mm
Warning | Sheet5.SchDoc | Off grid Pin J2-5 at 254.84mm,147.14mm
Warning | Sheet5.SchDoc | Off grid Pin J2-6 at 252.3mm,147.14mm
Warning | Sheet5.SchDoc | Off grid Pin J2-7 at 249.76mm,147.14mm
Warning | Sheet5.SchDoc | Off grid Pin J2-11 at 239.6mm,147.14mm
Warning | Sheet5.SchDoc | Off grid Pin J2-15 at 229.44mm,147.14mm
Warning | Sheet5.SchDoc | Off grid Pin J2-16 at 226.9mm,147.14mm
Warning | Sheet5.SchDoc | Off grid Pin J2-17 at 224.36mm,147.14mm
Warning | Sheet5.SchDoc | Off grid Pin J2-12 at 237.06mm,147.14mm
Warning | Sheet5.SchDoc | Off grid Pin J2-13 at 234.52mm,147.14mm
Warning | Sheet5.SchDoc | Off grid Pin J2-14 at 231.98mm,147.14mm
Error | Sheet2.SchDoc | Net NetU1_10 contains floating input pins (Pin U1-10)
