voltversa/Advanced-Smart-Home-Hub/firmware/Assets/previews/weather_gui_clear_day_preview.png

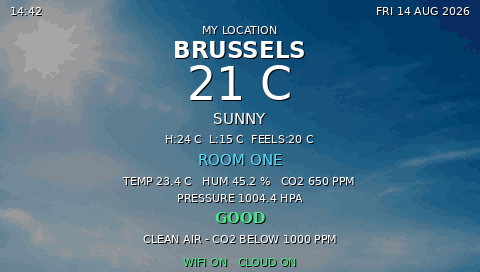
firmware/Assets/previews/weather_gui_clear_day_preview.png
