voltversa/Advanced-Smart-Home-Hub/firmware/Assets/previews/weather_gui_night_preview.png

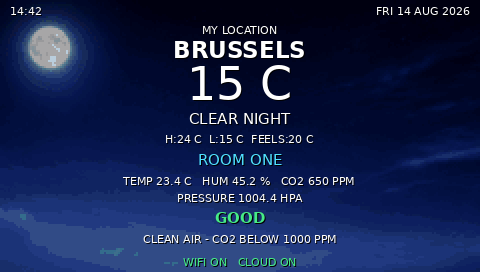
firmware/Assets/previews/weather_gui_night_preview.png
