voltversa/Advanced-Smart-Home-Hub/firmware/Assets/previews/weather_gui_sunset_preview.png

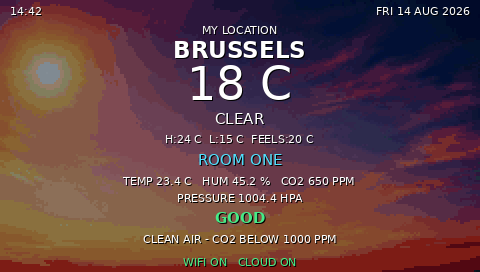
firmware/Assets/previews/weather_gui_sunset_preview.png
