voltversa/Advanced-Smart-Home-Hub/firmware/Assets/weather_generated/cloudy_480x272.png

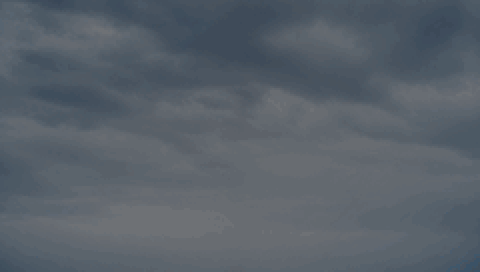
firmware/Assets/weather_generated/cloudy_480x272.png
