voltversa/Advanced-Smart-Home-Hub/firmware/Assets/weather_generated/night_480x272.png

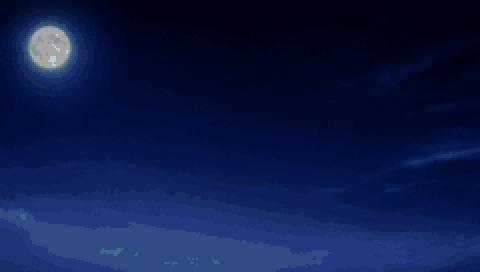
firmware/Assets/weather_generated/night_480x272.png
