voltversa/Advanced-Smart-Home-Hub/firmware/Assets/weather_generated/storm_480x272.png

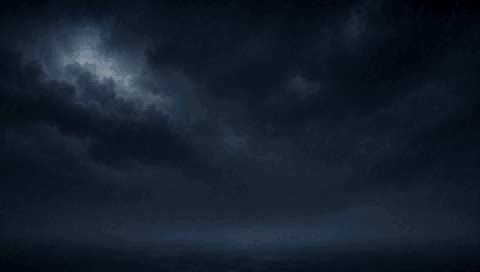
firmware/Assets/weather_generated/storm_480x272.png
