voltversa/Advanced-Smart-Home-Hub/firmware/Assets/weather_sources/clear_day_source.png

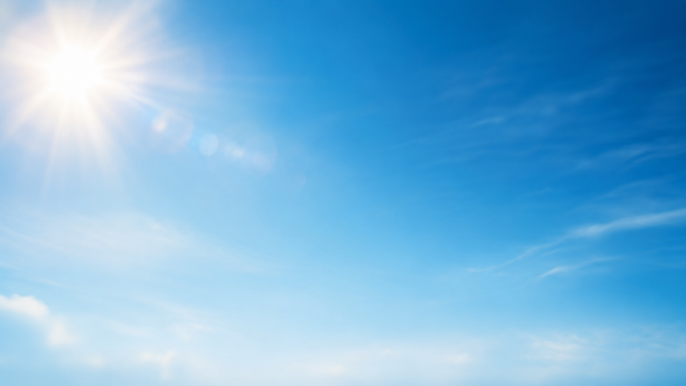
firmware/Assets/weather_sources/clear_day_source.png
