voltversa/Advanced-Smart-Home-Hub/firmware/Assets/weather_sources/cloudy_source.png

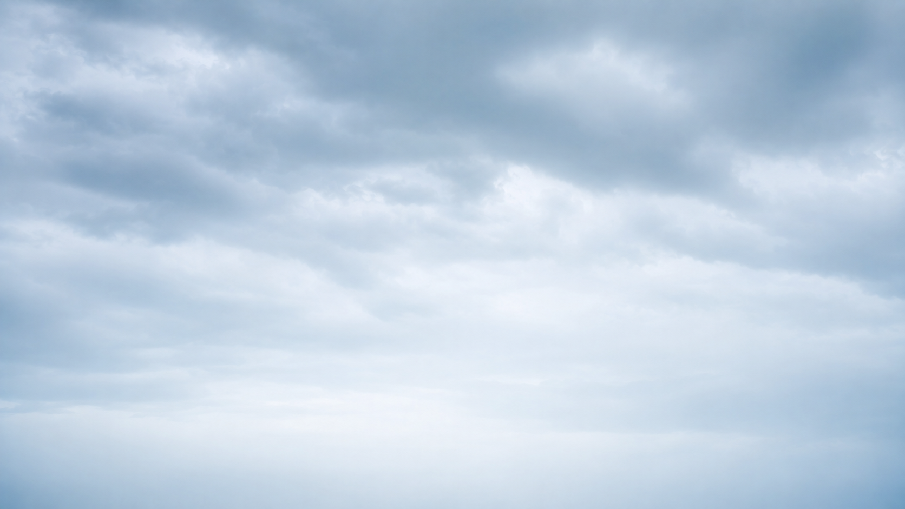
firmware/Assets/weather_sources/cloudy_source.png
