voltversa/Advanced-Smart-Home-Hub/submission/Mahmoud_Mostafa_Adv_pcb/images&videos/Screenshot 2026-08-16 113103.png

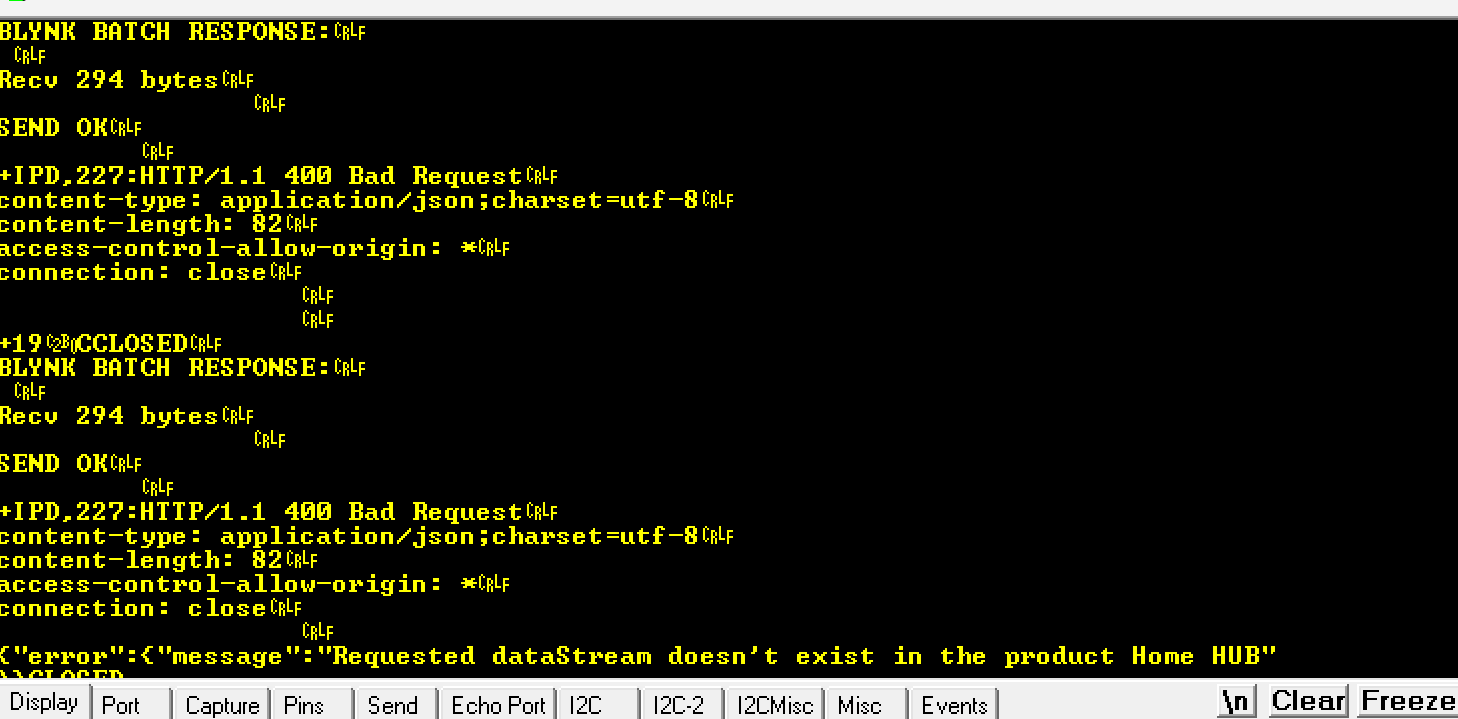
submission/Mahmoud_Mostafa_Adv_pcb/images&videos/Screenshot 2026-08-16 113103.png
