voltversa/Advanced-Smart-Home-Hub/submission/Mahmoud_Mostafa_Adv_pcb/images&videos/WhatsApp Image 2026-08-16 at 1.04.46 PM (1).jpeg

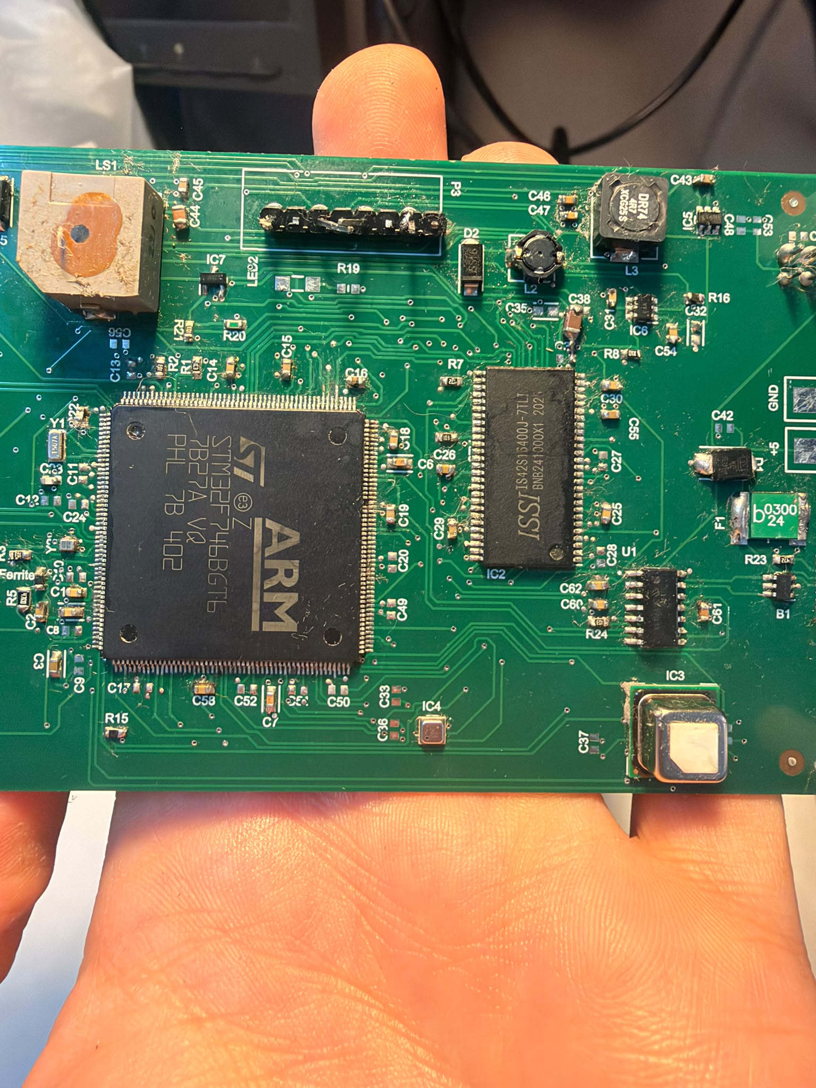
submission/Mahmoud_Mostafa_Adv_pcb/images&videos/WhatsApp Image 2026-08-16 at 1.04.46 PM (1).jpeg
