voltversa/Advanced-Smart-Home-Hub/submission/Mahmoud_Mostafa_Adv_pcb/PCB_3D_photo.png

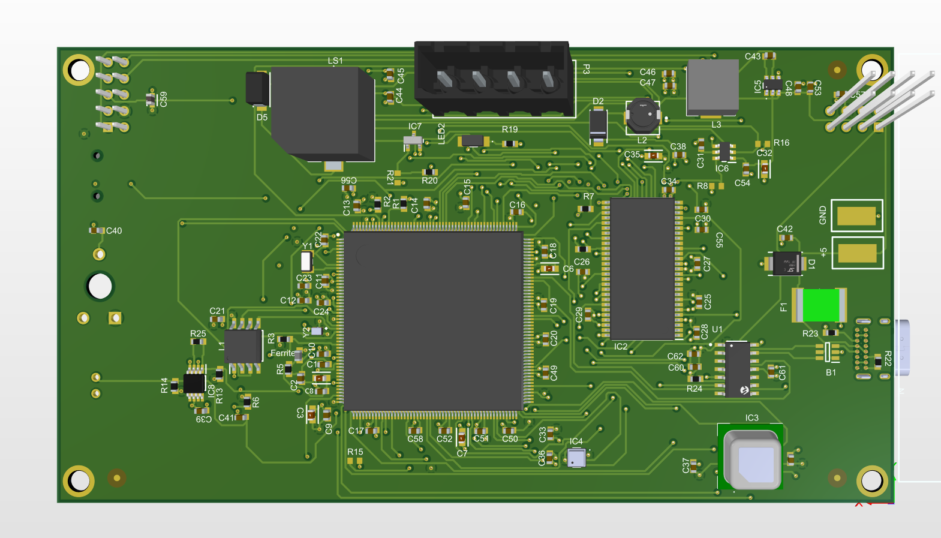
submission/Mahmoud_Mostafa_Adv_pcb/PCB_3D_photo.png
