voltversa/Advanced-Smart-Home-Hub/firmware/Core/Src/gui_modern_assets.c

#include "gui_modern_assets.h"

/* Rasterized DejaVu Sans glyphs and custom line icons. */
__attribute__((aligned(32)))
const uint8_t gui_modern_assets[GUI_MODERN_ASSET_BYTES] =
{
    0x4DU, 0x46U, 0x4EU, 0x54U, 0x01U, 0x00U, 0x3BU, 0x00U, 0x20U, 0x5AU, 0x03U, 0x07U, 0x14U, 0x14U, 0xFFU, 0xFFU, 0x0EU, 0x12U, 0x1CU, 0x0BU,
    0x0EU, 0x16U, 0xFFU, 0xFFU, 0x40U, 0x00U, 0x00U, 0x00U, 0x04U, 0x03U, 0x00U, 0x00U, 0xC8U, 0x05U, 0x00U, 0x00U, 0x8CU, 0x08U, 0x00U, 0x00U,
    0xB0U, 0x0AU, 0x00U, 0x00U, 0xF0U, 0x0EU, 0x00U, 0x00U, 0x4CU, 0x18U, 0x00U, 0x00U, 0xF0U, 0x19U, 0x00U, 0x00U, 0xFFU, 0xFFU, 0xFFU, 0xFFU,
    0xFFU, 0xFFU, 0xFFU, 0xFFU, 0x00U, 0x0BU, 0x04U, 0x00U, 0x04U, 0x01U, 0x00U, 0x00U, 0x00U, 0x00U, 0x00U, 0x00U, 0x00U, 0x03U, 0x04U, 0x08U,
    0x04U, 0x01U, 0x00U, 0x00U, 0x00U, 0x00U, 0x00U, 0x00U, 0x00U, 0x03U, 0x05U, 0x08U, 0x05U, 0x01U, 0x00U, 0x00U, 0x08U, 0x00U, 0x00U, 0x00U,
    0x00U, 0x03U, 0x09U, 0x08U, 0x09U, 0x02U, 0x00U, 0x00U, 0x10U, 0x00U, 0x00U, 0x00U, 0x00U, 0x03U, 0x07U, 0x0AU, 0x07U, 0x01U, 0x00U, 0x00U,
    0x20U, 0x00U, 0x00U, 0x00U, 0x00U, 0x03U, 0x0AU, 0x08U, 0x0AU, 0x02U, 0x00U, 0x00U, 0x2AU, 0x00U, 0x00U, 0x00U, 0x00U, 0x03U, 0x09U, 0x08U,
    0x09U, 0x02U, 0x00U, 0x00U, 0x3AU, 0x00U, 0x00U, 0x00U, 0x00U, 0x03U, 0x03U, 0x08U, 0x03U, 0x01U, 0x00U, 0x00U, 0x4AU, 0x00U, 0x00U, 0x00U,
    0x00U, 0x02U, 0x04U, 0x0AU, 0x04U, 0x01U, 0x00U, 0x00U, 0x52U, 0x00U, 0x00U, 0x00U, 0x00U, 0x02U, 0x04U, 0x0AU, 0x04U, 0x01U, 0x00U, 0x00U,
    0x5CU, 0x00U, 0x00U, 0x00U, 0x00U, 0x03U, 0x06U, 0x08U, 0x06U, 0x01U, 0x00U, 0x00U, 0x66U, 0x00U, 0x00U, 0x00U, 0x00U, 0x04U, 0x09U, 0x07U,
    0x09U, 0x02U, 0x00U, 0x00U, 0x6EU, 0x00U, 0x00U, 0x00U, 0x00U, 0x0AU, 0x04U, 0x02U, 0x04U, 0x01U, 0x00U, 0x00U, 0x7CU, 0x00U, 0x00U, 0x00U,
    0x00U, 0x07U, 0x04U, 0x04U, 0x04U, 0x01U, 0x00U, 0x00U, 0x7EU, 0x00U, 0x00U, 0x00U, 0x00U, 0x0AU, 0x04U, 0x01U, 0x04U, 0x01U, 0x00U, 0x00U,
    0x82U, 0x00U, 0x00U, 0x00U, 0x00U, 0x03U, 0x04U, 0x09U, 0x04U, 0x01U, 0x00U, 0x00U, 0x83U, 0x00U, 0x00U, 0x00U, 0x00U, 0x03U, 0x07U, 0x08U,
    0x07U, 0x01U, 0x00U, 0x00U, 0x8CU, 0x00U, 0x00U, 0x00U, 0x00U, 0x03U, 0x07U, 0x08U, 0x07U, 0x01U, 0x00U, 0x00U, 0x94U, 0x00U, 0x00U, 0x00U,
    0x00U, 0x03U, 0x07U, 0x08U, 0x07U, 0x01U, 0x00U, 0x00U, 0x9CU, 0x00U, 0x00U, 0x00U, 0x00U, 0x03U, 0x07U, 0x08U, 0x07U, 0x01U, 0x00U, 0x00U,
    0xA4U, 0x00U, 0x00U, 0x00U, 0x00U, 0x03U, 0x07U, 0x08U, 0x07U, 0x01U, 0x00U, 0x00U, 0xACU, 0x00U, 0x00U, 0x00U, 0x00U, 0x03U, 0x07U, 0x08U,
    0x07U, 0x01U, 0x00U, 0x00U, 0xB4U, 0x00U, 0x00U, 0x00U, 0x00U, 0x03U, 0x07U, 0x08U, 0x07U, 0x01U, 0x00U, 0x00U, 0xBCU, 0x00U, 0x00U, 0x00U,
    0x00U, 0x03U, 0x07U, 0x08U, 0x07U, 0x01U, 0x00U, 0x00U, 0xC4U, 0x00U, 0x00U, 0x00U, 0x00U, 0x03U, 0x07U, 0x08U, 0x07U, 0x01U, 0x00U, 0x00U,
    0xCCU, 0x00U, 0x00U, 0x00U, 0x00U, 0x03U, 0x07U, 0x08U, 0x07U, 0x01U, 0x00U, 0x00U, 0xD4U, 0x00U, 0x00U, 0x00U, 0x00U, 0x05U, 0x04U, 0x06U,
    0x04U, 0x01U, 0x00U, 0x00U, 0xDCU, 0x00U, 0x00U, 0x00U, 0x00U, 0x05U, 0x04U, 0x07U, 0x04U, 0x01U, 0x00U, 0x00U, 0xE2U, 0x00U, 0x00U, 0x00U,
    0x00U, 0x05U, 0x09U, 0x06U, 0x09U, 0x02U, 0x00U, 0x00U, 0xE9U, 0x00U, 0x00U, 0x00U, 0x00U, 0x06U, 0x09U, 0x05U, 0x09U, 0x02U, 0x00U, 0x00U,
    0xF5U, 0x00U, 0x00U, 0x00U, 0x00U, 0x05U, 0x09U, 0x06U, 0x09U, 0x02U, 0x00U, 0x00U, 0xFFU, 0x00U, 0x00U, 0x00U, 0x00U, 0x03U, 0x06U, 0x08U,
    0x06U, 0x01U, 0x00U, 0x00U, 0x0BU, 0x01U, 0x00U, 0x00U, 0x00U, 0x03U, 0x0BU, 0x0AU, 0x0BU, 0x02U, 0x00U, 0x00U, 0x13U, 0x01U, 0x00U, 0x00U,
    0x00U, 0x03U, 0x08U, 0x08U, 0x08U, 0x01U, 0x00U, 0x00U, 0x27U, 0x01U, 0x00U, 0x00U, 0x00U, 0x03U, 0x08U, 0x08U, 0x08U, 0x01U, 0x00U, 0x00U,
    0x2FU, 0x01U, 0x00U, 0x00U, 0x00U, 0x03U, 0x08U, 0x08U, 0x08U, 0x01U, 0x00U, 0x00U, 0x37U, 0x01U, 0x00U, 0x00U, 0x00U, 0x03U, 0x08U, 0x08U,
    0x08U, 0x01U, 0x00U, 0x00U, 0x3FU, 0x01U, 0x00U, 0x00U, 0x00U, 0x03U, 0x07U, 0x08U, 0x07U, 0x01U, 0x00U, 0x00U, 0x47U, 0x01U, 0x00U, 0x00U,
    0x00U, 0x03U, 0x06U, 0x08U, 0x06U, 0x01U, 0x00U, 0x00U, 0x4FU, 0x01U, 0x00U, 0x00U, 0x00U, 0x03U, 0x09U, 0x08U, 0x09U, 0x02U, 0x00U, 0x00U,
    0x57U, 0x01U, 0x00U, 0x00U, 0x00U, 0x03U, 0x08U, 0x08U, 0x08U, 0x01U, 0x00U, 0x00U, 0x67U, 0x01U, 0x00U, 0x00U, 0x00U, 0x03U, 0x03U, 0x08U,
    0x03U, 0x01U, 0x00U, 0x00U, 0x6FU, 0x01U, 0x00U, 0x00U, 0xFFU, 0x03U, 0x04U, 0x0AU, 0x03U, 0x01U, 0x00U, 0x00U, 0x77U, 0x01U, 0x00U, 0x00U,
    0x00U, 0x03U, 0x08U, 0x08U, 0x07U, 0x01U, 0x00U, 0x00U, 0x81U, 0x01U, 0x00U, 0x00U, 0x00U, 0x03U, 0x07U, 0x08U, 0x06U, 0x01U, 0x00U, 0x00U,
    0x89U, 0x01U, 0x00U, 0x00U, 0x00U, 0x03U, 0x09U, 0x08U, 0x09U, 0x02U, 0x00U, 0x00U, 0x91U, 0x01U, 0x00U, 0x00U, 0x00U, 0x03U, 0x08U, 0x08U,
    0x08U, 0x01U, 0x00U, 0x00U, 0xA1U, 0x01U, 0x00U, 0x00U, 0x00U, 0x03U, 0x09U, 0x08U, 0x09U, 0x02U, 0x00U, 0x00U, 0xA9U, 0x01U, 0x00U, 0x00U,
    0x00U, 0x03U, 0x07U, 0x08U, 0x07U, 0x01U, 0x00U, 0x00U, 0xB9U, 0x01U, 0x00U, 0x00U, 0x00U, 0x03U, 0x09U, 0x09U, 0x09U, 0x02U, 0x00U, 0x00U,
    0xC1U, 0x01U, 0x00U, 0x00U, 0x00U, 0x03U, 0x08U, 0x08U, 0x08U, 0x01U, 0x00U, 0x00U, 0xD3U, 0x01U, 0x00U, 0x00U, 0x00U, 0x03U, 0x07U, 0x08U,
    0x07U, 0x01U, 0x00U, 0x00U, 0xDBU, 0x01U, 0x00U, 0x00U, 0xFFU, 0x03U, 0x08U, 0x08U, 0x07U, 0x01U, 0x00U, 0x00U, 0xE3U, 0x01U, 0x00U, 0x00U,
    0x00U, 0x03U, 0x08U, 0x08U, 0x08U, 0x01U, 0x00U, 0x00U, 0xEBU, 0x01U, 0x00U, 0x00U, 0x00U, 0x03U, 0x08U, 0x08U, 0x08U, 0x01U, 0x00U, 0x00U,
    0xF3U, 0x01U, 0x00U, 0x00U, 0x00U, 0x03U, 0x0BU, 0x08U, 0x0BU, 0x02U, 0x00U, 0x00U, 0xFBU, 0x01U, 0x00U, 0x00U, 0x00U, 0x03U, 0x08U, 0x08U,
    0x08U, 0x01U, 0x00U, 0x00U, 0x0BU, 0x02U, 0x00U, 0x00U, 0xFFU, 0x03U, 0x08U, 0x08U, 0x07U, 0x01U, 0x00U, 0x00U, 0x13U, 0x02U, 0x00U, 0x00U,
    0x00U, 0x03U, 0x08U, 0x08U, 0x08U, 0x01U, 0x00U, 0x00U, 0x1BU, 0x02U, 0x00U, 0x00U, 0x00U, 0x0EU, 0x05U, 0x00U, 0x05U, 0x01U, 0x00U, 0x00U,
    0x00U, 0x00U, 0x00U, 0x00U, 0x00U, 0x03U, 0x06U, 0x0BU, 0x06U, 0x01U, 0x00U, 0x00U, 0x00U, 0x00U, 0x00U, 0x00U, 0x00U, 0x03U, 0x07U, 0x0BU,
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
};
