voltversa/Advanced-Smart-Home-Hub/firmware/Core/Inc/gui_modern_assets.h

#ifndef GUI_MODERN_ASSETS_H
#define GUI_MODERN_ASSETS_H

#include <stdint.h>

#define GUI_MODERN_ASSET_BYTES  6640UL

extern const uint8_t gui_modern_assets[GUI_MODERN_ASSET_BYTES];

#endif /* GUI_MODERN_ASSETS_H */
